0kam/picowatt/app/src/picowatt/plots.py

"""Stacked V/I/P realtime plots with min/max decimation."""

from __future__ import annotations

import numpy as np
import pyqtgraph as pg

from .buffer import ChannelBuffer
from .decimate import minmax_decimate

CH_COLORS = ("#4fc3f7", "#ffb74d")  # ch0 input, ch1 output
CH_NAMES = ("in", "out")
MAX_PLOT_POINTS = 2000


class LivePlots(pg.GraphicsLayoutWidget):
    """Three stacked plots (V / I / P), linked X axes, per-channel curves."""

    def __init__(self) -> None:
        super().__init__()
        pg.setConfigOptions(antialias=False)
        self.plots: list[pg.PlotItem] = []
        labels = [("Voltage", "V"), ("Current", "A"), ("Power", "W")]
        for row, (name, unit) in enumerate(labels):
            p = self.addPlot(row=row, col=0)
            p.setLabel("left", name, units=unit)
            p.showGrid(x=True, y=True, alpha=0.2)
            p.setClipToView(True)
            # Y range follows only the visible data; no "ks"-style prefix on time
            p.getViewBox().setAutoVisible(y=True)
            p.getAxis("bottom").enableAutoSIPrefix(False)
            if row > 0:
                p.setXLink(self.plots[0])
            if row < 2:
                p.getAxis("bottom").setStyle(showValues=False)
            self.plots.append(p)
        self.plots[2].setLabel("bottom", "Time [s]")

        # curves[plot_row][ch]
        self.curves = [
            [p.plot(pen=pg.mkPen(CH_COLORS[c], width=1), name=CH_NAMES[c]) for c in (0, 1)]
            for p in self.plots
        ]

        # Region selector on the power plot for energy integration.
        self.region = pg.LinearRegionItem(brush=(80, 200, 120, 40))
        self.region.setZValue(10)
        self.region.setVisible(False)
        self.plots[2].addItem(self.region)

    def show_region(self, visible: bool) -> None:
        if visible:
            (x0, x1) = self.plots[0].viewRange()[0]
            span = x1 - x0
            self.region.setRegion((x0 + span * 0.3, x0 + span * 0.7))
        self.region.setVisible(visible)

    def region_bounds(self) -> tuple[float, float]:
        lo, hi = self.region.getRegion()
        return float(lo), float(hi)

    def update_channel(self, ch: int, buf: ChannelBuffer, t0: float, t1: float) -> None:
        t, v, i = buf.window(t0, t1)
        if len(t) == 0:
            for row in range(3):
                self.curves[row][ch].setData([], [])
            return
        p = v * i
        for row, y in enumerate((v, i, p)):
            td, yd = minmax_decimate(t, y.astype(np.float64), MAX_PLOT_POINTS)
            self.curves[row][ch].setData(td, yd)

    def set_x_range(self, t0: float, t1: float) -> None:
        self.plots[0].setXRange(t0, t1, padding=0)

    def reset_view(self) -> None:
        """Re-enable Y autorange on all plots (X is driven by follow mode)."""
        for p in self.plots:
            p.enableAutoRange(axis="y")
            p.getViewBox().setAutoVisible(y=True)
